neez11/Smart-Home-Alarm/backend/smart_alarm/logger.py

import logging
from logging.handlers import RotatingFileHandler
from pathlib import Path


def setup_logger(name: str = "smart_alarm") -> logging.Logger:
    logs_dir = Path("logs")
    logs_dir.mkdir(exist_ok=True)

    logger = logging.getLogger(name)
    logger.setLevel(logging.INFO)

    if logger.handlers:
        return logger

    formatter = logging.Formatter(
        "%(asctime)s | %(levelname)s | %(name)s | %(message)s"
    )

    file_handler = RotatingFileHandler(
        logs_dir / "backend.log",
        maxBytes=1_000_000,
        backupCount=3,
        encoding="utf-8"
    )
    file_handler.setLevel(logging.INFO)
    file_handler.setFormatter(formatter)

    stream_handler = logging.StreamHandler()
    stream_handler.setLevel(logging.INFO)
    stream_handler.setFormatter(formatter)

    logger.addHandler(file_handler)
    logger.addHandler(stream_handler)

    return logger
